Seaforged/Sentry-RF/include/display.h

#ifndef DISPLAY_H
#define DISPLAY_H

#include <Adafruit_SSD1306.h>
#include "detection_types.h"

static const int SCREEN_WIDTH  = 128;
static const int SCREEN_HEIGHT = 64;

// Phase J: SCREEN_RID added on every board with a WiFi scanner (all three).
// Layout: 0=Dashboard, 1=Spectrum, 2=GPS, 3=Integrity, 4=Threat, 5=System,
// 6=RID, (LR1121 only) 7=Spectrum24.
#ifdef BOARD_T3S3_LR1121
static const int NUM_SCREENS = 8;
#else
static const int NUM_SCREENS = 7;
#endif

// RSSI range for bar chart vertical scaling
// LR1121 noise floor is ~-127 dBm (lower than SX1262's ~-110), so -130 ensures
// even quiet channels show a small bar instead of nothing
static const float DISPLAY_RSSI_MIN = -130.0;
static const float DISPLAY_RSSI_MAX = -40.0;

void displayInit(Adafruit_SSD1306& disp);
void displayBootSplash(Adafruit_SSD1306& disp);

// Fatal-error screen with version header and up to two info lines.
// Caller is expected to halt (e.g. for(;;) delay(1000);) after this call.
void displayFatalError(Adafruit_SSD1306& disp, const char* line1, const char* line2 = nullptr);

// Non-fatal warning screen — boot continues. Caller typically delay(3000)
// after this call so the operator has time to read the message before the
// display task overwrites it with the dashboard.
void displayWarning(Adafruit_SSD1306& disp, const char* line1, const char* line2 = nullptr);

// Phase K: boot self-test summary. Caller delays 3 s after rendering so the
// operator can read the result before the main UI takes over. radioOK /
// antennaOK are the self-test outcomes; gpsLine is a caller-provided status
// string (usually "Acquiring...") since GPS is checked asynchronously.
void displayBootSummary(Adafruit_SSD1306& disp, bool radioOK, bool antennaOK,
                        const char* gpsLine);

// Screen 0: Dashboard summary — all-in-one glance
void screenDashboard(Adafruit_SSD1306& disp, const SystemState& state, int page);

// Screen 1: Sub-GHz spectrum bar chart
void screenSpectrum(Adafruit_SSD1306& disp, const SystemState& state, int page);

// Screen 2: GPS + compass
void screenGPS(Adafruit_SSD1306& disp, const SystemState& state, int page);

// Screen 3: GNSS integrity
void screenIntegrity(Adafruit_SSD1306& disp, const SystemState& state, int page);

// Screen 4: Threat detail
void screenThreat(Adafruit_SSD1306& disp, const SystemState& state, int page);

// Screen 5: System info
void screenSystem(Adafruit_SSD1306& disp, const SystemState& state, int page);

// Screen 6: ASTM F3411 Remote ID decoded payload (Phase J)
void screenRID(Adafruit_SSD1306& disp, const SystemState& state, int page);

// Screen 7: 2.4 GHz spectrum (LR1121 only)
void screenSpectrum24(Adafruit_SSD1306& disp, const SystemState& state, int page);

void drawPageDots(Adafruit_SSD1306& disp, int current, int total);

#endif // DISPLAY_H
